mihai9002/RFR2/Images/Checkouts/sigmanortec.png

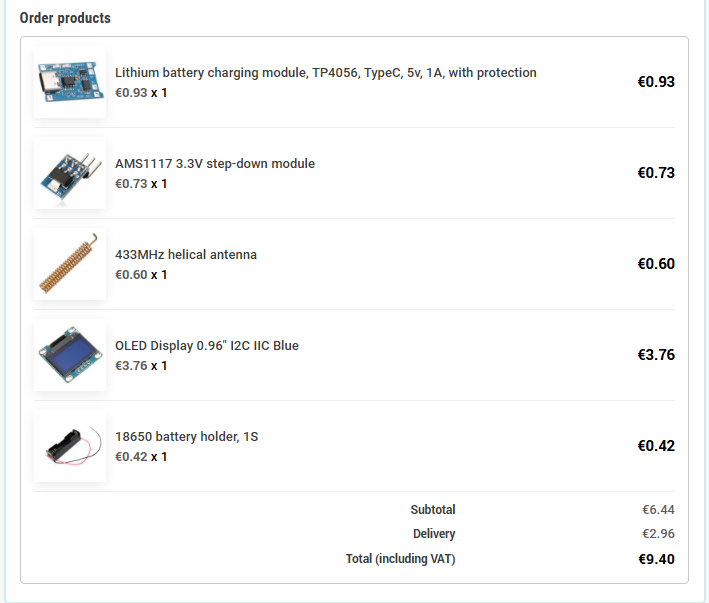
Images/Checkouts/sigmanortec.png
